szymonwilczek/talos-7/firmware/include/firmware_version.h

#ifndef FIRMWARE_VERSION_H
#define FIRMWARE_VERSION_H

#define FW_VERSION_MAJOR 2
#define FW_VERSION_MINOR 8
#define FW_VERSION_PATCH 0

#define FW_BUILD_DATE "2025-11-23"

#endif // FIRMWARE_VERSION_H
