szymonwilczek/talos-7/firmware/include/easter_egg.h

#ifndef EASTER_EGG_H
#define EASTER_EGG_H

#include <stdbool.h>

/**
 * @brief Runs the Atari Breakout game.
 *
 * Blocking function. Exits when Button 1 is pressed.
 */
void run_game_breakout(void);

#endif // EASTER_EGG_H
