szymonwilczek/talos-7/firmware/include/assets_graphics.h

#ifndef ASSETS_GRAPHICS_H
#define ASSETS_GRAPHICS_H

#include <stdint.h>

// --- TALOS LOGO (8x8 Mini) ---
static const uint8_t talos_logo_8x8[8] = {0x0F, 0x09, 0xFD, 0x01,
                                          0x01, 0xDD, 0x09, 0x0F};

// Talos 7 Favicon (16x16 pixel grid)
static const uint8_t talos_favicon_16x16[] = {
    0x3e, 0x22, 0x22, 0x12, 0x12, 0xf2, 0xf2, 0x00, 0x00, 0xf2, 0xf2,
    0x12, 0x12, 0x22, 0x22, 0x3e, 0x00, 0x00, 0x00, 0x00, 0x00, 0x7f,
    0x7f, 0x00, 0x00, 0x7d, 0x7d, 0x00, 0x00, 0x00, 0x00, 0x00};

// Talos 7 Boot Logo (32x32 pixel grid)
// Format: 4 pages (rows 8px) for 32 columns. Total: 128 bytes.
static const uint8_t talos_boot_logo_32x32[] = {
    // page 0
    0xfc, 0xfc, 0x0c, 0x0c, 0x0c, 0x0c, 0x8c, 0x8c, 0x8c, 0x8c, 0x8c, 0x8c,
    0x8c, 0x8c, 0x00, 0x00, 0x00, 0x00, 0x8c, 0x8c, 0x8c, 0x8c, 0x8c, 0x8c,
    0x8c, 0x8c, 0x0c, 0x0c, 0x0c, 0x0c, 0xfc, 0xfc,
    // page 1
    0x07, 0x07, 0x06, 0x06, 0x06, 0x07, 0x03, 0x01, 0x01, 0x01, 0xff, 0xff,
    0xff, 0xff, 0x00, 0x00, 0x00, 0x00, 0xff, 0xff, 0xff, 0xff, 0x01, 0x01,
    0x01, 0x03, 0x07, 0x06, 0x06, 0x06, 0x07, 0x07,
    // page 2
    0x00, 0x00, 0x00, 0x00, 0x00, 0x00, 0x00, 0x00, 0x00, 0x00, 0xff, 0xff,
    0xff, 0xff, 0x00, 0x00, 0x00, 0x00, 0xf8, 0xf8, 0xf8, 0xf8, 0x00, 0x00,
    0x00, 0x00, 0x00, 0x00, 0x00, 0x00, 0x00, 0x00,
    // page 3
    0x00, 0x00, 0x00, 0x00, 0x00, 0x00, 0x00, 0x00, 0x00, 0x00, 0x7f, 0x7f,
    0x7f, 0x7f, 0x00, 0x00, 0x00, 0x00, 0x7f, 0x7f, 0x7f, 0x7f, 0x00, 0x00,
    0x00, 0x00, 0x00, 0x00, 0x00, 0x00, 0x00, 0x00};

// Space Invaders - Aliens (8x8) - Hands up
static const uint8_t invader_frame1[8] = {0x18, 0x3C, 0x7E, 0xDB,
                                          0xFF, 0x24, 0x5A, 0xA5};

// Space Invaders - Aliens (8x8) - Hands down
static const uint8_t invader_frame2[8] = {0x18, 0x3C, 0x7E, 0xDB,
                                          0xFF, 0x5A, 0x81, 0x42};

// Space Invaders - Cannon (8x8)
static const uint8_t cannon_bitmap[8] = {0x00, 0x00, 0x7E, 0x3C,
                                         0x18, 0x3C, 0x7E, 0x00};

#endif // ASSETS_GRAPHICS_H
