szymonwilczek/talos-7/firmware/include/emoji.h

#ifndef EMOJI_H
#define EMOJI_H

static const uint8_t emoji_bitmaps[21][8] = {
    // 0: 🎮 (controller)
    {0x38, 0x44, 0x94, 0x44, 0x46, 0x95, 0x44, 0x38},
    // 1: 💼 (briefcase)
    {0x7c, 0x46, 0x4a, 0x5a, 0x5a, 0x4a, 0x46, 0x7c},
    // 2: 🏠 (home)
    {0x10, 0xf8, 0x8c, 0xe6, 0x86, 0x8c, 0xf8, 0x10},
    // 3: 🔧 (settings - wrench)
    {0x00, 0x00, 0xc7, 0x7c, 0x7c, 0xc7, 0x00, 0x00},
    // 4: ⚡ (lightning)
    {0x00, 0x80, 0xc8, 0x6c, 0x3e, 0x1b, 0x09, 0x00},
    // 5: 📧 (mail)
    {0x00, 0x3e, 0x41, 0x5d, 0x51, 0x4e, 0x20, 0x00},
    // 6: 💻 (computer)
    {0x3e, 0x22, 0xa2, 0xe2, 0xe2, 0xa2, 0x22, 0x3e},
    // 7: 🎵 (music note)
    {0xc0, 0xfe, 0xc2, 0x02, 0x62, 0x7e, 0x60, 0x00},
    // 8: 📝 (note)
    {0xc0, 0xa0, 0x50, 0x28, 0x1c, 0x0a, 0x07, 0x03},
    // 9: ☕ (coffee cup)
    {0x7e, 0xc2, 0xc2, 0xc2, 0xc2, 0xfe, 0x64, 0x3c},
    // 10: 🗡️ (sword)
    {0xd8, 0xf0, 0x78, 0x7c, 0x5e, 0x0f, 0x07, 0x03},
    // 11: ❤️ (heart)
    {0x00, 0x0c, 0x12, 0x22, 0x44, 0x22, 0x12, 0x0c},
    // 12: 🔔 (bell)
    {0x40, 0x7c, 0xc6, 0xc6, 0x7c, 0x40, 0x00, 0x00},
    // 13: 🧪 (lab probe)
    {0x40, 0xa0, 0x91, 0x8f, 0x8f, 0x91, 0xa0, 0x40},
    // 14: 🔒 (lock)
    {0x78, 0xfe, 0xf9, 0xc9, 0xf9, 0xfe, 0x78, 0x00},
    // 15: ☂️ (umbrella)
    {0x0c, 0x0e, 0x4f, 0x8f, 0x7f, 0x0f, 0x0e, 0x0c},
    // 16: 🦕 (dinosaur)
    {0x06, 0x15, 0xff, 0x7d, 0xff, 0x40, 0x30, 0x00},
    // 17: 👻 (ghost)
    {0x3e, 0x45, 0x47, 0xf5, 0xcf, 0x83, 0x82, 0x84},
    // 18: 🔫 (pistol)
    {0x07, 0x06, 0x06, 0x0e, 0x16, 0x96, 0xfe, 0x7c},
    // 19: ⏳ (hourglass)
    {0x82, 0xee, 0x92, 0x92, 0x92, 0xee, 0x82, 0x00},
    // 20: 🌷 (tulip)
    {0x20, 0x4f, 0x9e, 0xff, 0x9e, 0x4f, 0x20, 0x00},
};

#define MAX_EMOJIS 21
static const char *emoji_strings[MAX_EMOJIS] = {
    "🎮", "💼", "🏠", "🔧", "⚡", "📧", "💻", "🎵", "📝", "☕", "🗡️",
    "❤️",  "🔔", "🧪", "🔒", "☂️",  "🦕", "👻", "🔫", "⏳", "🌷"};

static const uint8_t os_icons[3][8] = {
    // 0: Linux
    {0x20, 0xfe, 0x37, 0x33, 0x3f, 0xf7, 0xf3, 0xff},
    // 1: Windows
    {0x00, 0xee, 0xee, 0xee, 0x00, 0xee, 0xee, 0xee},
    // 2: macOS
    {0x38, 0xfc, 0xfc, 0x7a, 0xfd, 0xfc, 0x48, 0x00},
};

#endif // EMOJI_H
