szymonwilczek/talos-7/firmware/include/tusb_config.h

#ifndef _TUSB_CONFIG_H_
#define _TUSB_CONFIG_H_

#ifdef __cplusplus
extern "C" {
#endif

//--------------------------------------------------------------------+
// Board Specific Configuration
//--------------------------------------------------------------------+

#ifndef BOARD_TUD_RHPORT
#define BOARD_TUD_RHPORT 0
#endif

#ifndef BOARD_TUD_MAX_SPEED
#define BOARD_TUD_MAX_SPEED OPT_MODE_FULL_SPEED
#endif

//--------------------------------------------------------------------+
// COMMON CONFIGURATION
//--------------------------------------------------------------------+

// defined by compiler flags for flexibility
#ifndef CFG_TUSB_MCU
#define CFG_TUSB_MCU OPT_MCU_RP2040
#endif

#ifndef CFG_TUSB_OS
#define CFG_TUSB_OS OPT_OS_NONE
#endif

#ifndef CFG_TUSB_DEBUG
#define CFG_TUSB_DEBUG 0
#endif

#ifndef CFG_TUSB_MEM_SECTION
#define CFG_TUSB_MEM_SECTION
#endif

#ifndef CFG_TUSB_MEM_ALIGN
#define CFG_TUSB_MEM_ALIGN __attribute__((aligned(4)))
#endif

//--------------------------------------------------------------------+
// DEVICE CONFIGURATION
//--------------------------------------------------------------------+

#ifndef CFG_TUD_ENDPOINT0_SIZE
#define CFG_TUD_ENDPOINT0_SIZE 64
#endif

//------------- CLASS -------------//
#define CFG_TUD_HID 1
#define CFG_TUD_CDC 1
#define CFG_TUD_MSC 0
#define CFG_TUD_MIDI 1
#define CFG_TUD_VENDOR 0

// HID buffer size should be sufficient to hold ID (if any) + Data
#define CFG_TUD_HID_EP_BUFSIZE 16

// CDC FIFO size of TX and RX
#define CFG_TUD_CDC_RX_BUFSIZE 256
#define CFG_TUD_CDC_TX_BUFSIZE 256
#define CFG_TUD_MIDI_RX_BUFSIZE 64
#define CFG_TUD_MIDI_TX_BUFSIZE 64

// CDC Endpoint transfer buffer size, more is faster
#define CFG_TUD_CDC_EP_BUFSIZE 64

//--------------------------------------------------------------------+
// DEVICE MODE CONFIGURATION
//--------------------------------------------------------------------+

#define CFG_TUSB_RHPORT0_MODE (OPT_MODE_DEVICE | OPT_MODE_FULL_SPEED)

#ifdef __cplusplus
}
#endif

#endif /* _TUSB_CONFIG_H_ */
