szymonwilczek/talos-7/firmware/tests/test_macro_config.c

/*
 * unit tests for macro_config.c
 *
 * tests: CRC32 algorithm, layer switching logic, factory defaults structure
 *
 * note: this file contains copied logic from macro_config.c to avoid
 * complex mocking of flash/watchdog. i did test the algorithms myself.
 */

#include "unity/unity.h"

#include <stddef.h>
#include <stdint.h>
#include <string.h>

// copied constants from firmware
#define NUM_BUTTONS 7
#define MAX_LAYERS 4
#define MAX_SEQUENCE_STEPS 16
#define MAX_SCRIPT_SIZE 512
#define MAX_LAYER_NAME_LEN 16
#define MAX_MACRO_NAME_LEN 16

// copied macro types
typedef enum {
  MACRO_TYPE_KEY_PRESS = 0,
  MACRO_TYPE_KEY_SEQUENCE = 1,
  MACRO_TYPE_TEXT_STRING = 2,
  MACRO_TYPE_LAYER_TOGGLE = 3,
  MACRO_TYPE_MOUSE_MOVE = 4,
  MACRO_TYPE_MOUSE_CLICK = 5,
  MACRO_TYPE_SCRIPT = 6,
  MACRO_TYPE_MIDI_NOTE = 7,
  MACRO_TYPE_MIDI_CC = 8
} macro_type_t;

// copied key step structure
typedef struct {
  uint8_t keycode;
  uint8_t modifiers;
} key_step_t;

// copied macro entry structure
typedef struct {
  macro_type_t type;
  uint8_t value;
  char macro_string[64];
  char name[MAX_MACRO_NAME_LEN];
  uint8_t emoji_index;
  key_step_t sequence[MAX_SEQUENCE_STEPS];
  uint8_t sequence_length;
  uint8_t repeat_count;
  uint16_t repeat_interval;
  int8_t mouse_x;
  int8_t mouse_y;
  uint8_t midiNote;
  uint8_t midiVelocity;
  uint8_t midiChannel;
  uint8_t midiCCNumber;
  uint8_t midiCCValue;
  char script[MAX_SCRIPT_SIZE];
  uint8_t script_platform;
  key_step_t terminal_shortcut[MAX_SEQUENCE_STEPS];
  uint8_t terminal_shortcut_length;
} macro_entry_t;

// copied config structure
typedef struct {
  macro_entry_t macros[MAX_LAYERS][NUM_BUTTONS];
  char layer_names[MAX_LAYERS][MAX_LAYER_NAME_LEN];
  uint8_t layer_emojis[MAX_LAYERS];
  uint8_t current_layer;
  uint8_t oled_timeout;
  uint32_t crc32;
} config_data_t;

// copied CRC32 table from macro_config.c
static const uint32_t crc32_table[256] = {
    0x00000000, 0x77073096, 0xEE0E612C, 0x990951BA, 0x076DC419, 0x706AF48F,
    0xE963A535, 0x9E6495A3, 0x0EDB8832, 0x79DCB8A4, 0xE0D5E91E, 0x97D2D988,
    0x09B64C2B, 0x7EB17CBD, 0xE7B82D07, 0x90BF1D91, 0x1DB71064, 0x6AB020F2,
    0xF3B97148, 0x84BE41DE, 0x1ADAD47D, 0x6DDDE4EB, 0xF4D4B551, 0x83D385C7,
    0x136C9856, 0x646BA8C0, 0xFD62F97A, 0x8A65C9EC, 0x14015C4F, 0x63066CD9,
    0xFA0F3D63, 0x8D080DF5, 0x3B6E20C8, 0x4C69105E, 0xD56041E4, 0xA2677172,
    0x3C03E4D1, 0x4B04D447, 0xD20D85FD, 0xA50AB56B, 0x35B5A8FA, 0x42B2986C,
    0xDBBBC9D6, 0xACBCF940, 0x32D86CE3, 0x45DF5C75, 0xDCD60DCF, 0xABD13D59,
    0x26D930AC, 0x51DE003A, 0xC8D75180, 0xBFD06116, 0x21B4F4B5, 0x56B3C423,
    0xCFBA9599, 0xB8BDA50F, 0x2802B89E, 0x5F058808, 0xC60CD9B2, 0xB10BE924,
    0x2F6F7C87, 0x58684C11, 0xC1611DAB, 0xB6662D3D, 0x76DC4190, 0x01DB7106,
    0x98D220BC, 0xEFD5102A, 0x71B18589, 0x06B6B51F, 0x9FBFE4A5, 0xE8B8D433,
    0x7807C9A2, 0x0F00F934, 0x9609A88E, 0xE10E9818, 0x7F6A0DBB, 0x086D3D2D,
    0x91646C97, 0xE6635C01, 0x6B6B51F4, 0x1C6C6162, 0x856530D8, 0xF262004E,
    0x6C0695ED, 0x1B01A57B, 0x8208F4C1, 0xF50FC457, 0x65B0D9C6, 0x12B7E950,
    0x8BBEB8EA, 0xFCB9887C, 0x62DD1DDF, 0x15DA2D49, 0x8CD37CF3, 0xFBD44C65,
    0x4DB26158, 0x3AB551CE, 0xA3BC0074, 0xD4BB30E2, 0x4ADFA541, 0x3DD895D7,
    0xA4D1C46D, 0xD3D6F4FB, 0x4369E96A, 0x346ED9FC, 0xAD678846, 0xDA60B8D0,
    0x44042D73, 0x33031DE5, 0xAA0A4C5F, 0xDD0D7CC9, 0x5005713C, 0x270241AA,
    0xBE0B1010, 0xC90C2086, 0x5768B525, 0x206F85B3, 0xB966D409, 0xCE61E49F,
    0x5EDEF90E, 0x29D9C998, 0xB0D09822, 0xC7D7A8B4, 0x59B33D17, 0x2EB40D81,
    0xB7BD5C3B, 0xC0BA6CAD, 0xEDB88320, 0x9ABFB3B6, 0x03B6E20C, 0x74B1D29A,
    0xEAD54739, 0x9DD277AF, 0x04DB2615, 0x73DC1683, 0xE3630B12, 0x94643B84,
    0x0D6D6A3E, 0x7A6A5AA8, 0xE40ECF0B, 0x9309FF9D, 0x0A00AE27, 0x7D079EB1,
    0xF00F9344, 0x8708A3D2, 0x1E01F268, 0x6906C2FE, 0xF762575D, 0x806567CB,
    0x196C3671, 0x6E6B06E7, 0xFED41B76, 0x89D32BE0, 0x10DA7A5A, 0x67DD4ACC,
    0xF9B9DF6F, 0x8EBEEFF9, 0x17B7BE43, 0x60B08ED5, 0xD6D6A3E8, 0xA1D1937E,
    0x38D8C2C4, 0x4FDFF252, 0xD1BB67F1, 0xA6BC5767, 0x3FB506DD, 0x48B2364B,
    0xD80D2BDA, 0xAF0A1B4C, 0x36034AF6, 0x41047A60, 0xDF60EFC3, 0xA867DF55,
    0x316E8EEF, 0x4669BE79, 0xCB61B38C, 0xBC66831A, 0x256FD2A0, 0x5268E236,
    0xCC0C7795, 0xBB0B4703, 0x220216B9, 0x5505262F, 0xC5BA3BBE, 0xB2BD0B28,
    0x2BB45A92, 0x5CB36A04, 0xC2D7FFA7, 0xB5D0CF31, 0x2CD99E8B, 0x5BDEAE1D,
    0x9B64C2B0, 0xEC63F226, 0x756AA39C, 0x026D930A, 0x9C0906A9, 0xEB0E363F,
    0x72076785, 0x05005713, 0x95BF4A82, 0xE2B87A14, 0x7BB12BAE, 0x0CB61B38,
    0x92D28E9B, 0xE5D5BE0D, 0x7CDCEFB7, 0x0BDBDF21, 0x86D3D2D4, 0xF1D4E242,
    0x68DDB3F8, 0x1FDA836E, 0x81BE16CD, 0xF6B9265B, 0x6FB077E1, 0x18B74777,
    0x88085AE6, 0xFF0F6A70, 0x66063BCA, 0x11010B5C, 0x8F659EFF, 0xF862AE69,
    0x616BFFD3, 0x166CCF45, 0xA00AE278, 0xD70DD2EE, 0x4E048354, 0x3903B3C2,
    0xA7672661, 0xD06016F7, 0x4969474D, 0x3E6E77DB, 0xAED16A4A, 0xD9D65ADC,
    0x40DF0B66, 0x37D83BF0, 0xA9BCAE53, 0xDEBB9EC5, 0x47B2CF7F, 0x30B5FFE9,
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

// copied CRC calculation function
static uint32_t test_calculate_crc(const config_data_t *config) {
  uint32_t crc = 0xFFFFFFFF;
  const uint8_t *data = (const uint8_t *)config;
  size_t len = offsetof(config_data_t, crc32);

  for (size_t i = 0; i < len; i++) {
    crc = crc32_table[(crc ^ data[i]) & 0xFF] ^ (crc >> 8);
  }

  return ~crc;
}

// layer switching simulation
static uint8_t g_test_layer = 0;

static uint8_t test_get_layer(void) { return g_test_layer; }

static void test_cycle_layer(void) {
  g_test_layer = (g_test_layer + 1) % MAX_LAYERS;
}

static void test_set_layer(uint8_t layer) {
  if (layer < MAX_LAYERS) {
    g_test_layer = layer;
  }
}

// factory defaults simulation
static void test_set_factory_defaults(config_data_t *config) {
  memset(config, 0, sizeof(config_data_t));

  // set layer names
  snprintf(config->layer_names[0], MAX_LAYER_NAME_LEN, "Main");
  snprintf(config->layer_names[1], MAX_LAYER_NAME_LEN, "Work");
  snprintf(config->layer_names[2], MAX_LAYER_NAME_LEN, "Home");
  snprintf(config->layer_names[3], MAX_LAYER_NAME_LEN, "Media");

  // set emojis
  config->layer_emojis[0] = 0;
  config->layer_emojis[1] = 1;
  config->layer_emojis[2] = 2;
  config->layer_emojis[3] = 7;

  // button 7 (index 6) is layer toggle
  for (int layer = 0; layer < MAX_LAYERS; layer++) {
    config->macros[layer][6].type = MACRO_TYPE_LAYER_TOGGLE;
  }

  config->oled_timeout = 60;
}

// ==================== CRC32 TESTS ====================

void test_crc32_nonzero_for_zeroed_config(void) {
  config_data_t config;
  memset(&config, 0, sizeof(config));

  uint32_t crc = test_calculate_crc(&config);

  // crc of zeroed data should still produce a valid checksum
  TEST_ASSERT_TRUE(crc != 0);
}

void test_crc32_different_for_different_data(void) {
  config_data_t config1;
  config_data_t config2;

  memset(&config1, 0, sizeof(config1));
  memset(&config2, 0, sizeof(config2));

  config2.current_layer = 1;

  uint32_t crc1 = test_calculate_crc(&config1);
  uint32_t crc2 = test_calculate_crc(&config2);

  TEST_ASSERT_NOT_EQUAL(crc1, crc2);
}

void test_crc32_same_for_identical_data(void) {
  config_data_t config1;
  config_data_t config2;

  memset(&config1, 0xAB, sizeof(config1));
  memset(&config2, 0xAB, sizeof(config2));

  uint32_t crc1 = test_calculate_crc(&config1);
  uint32_t crc2 = test_calculate_crc(&config2);

  TEST_ASSERT_EQUAL(crc1, crc2);
}

void test_crc32_changes_with_any_byte(void) {
  config_data_t config1;
  config_data_t config2;

  memset(&config1, 0, sizeof(config1));
  memset(&config2, 0, sizeof(config2));

  // change just one byte in macro name
  config2.macros[0][0].name[0] = 'X';

  uint32_t crc1 = test_calculate_crc(&config1);
  uint32_t crc2 = test_calculate_crc(&config2);

  TEST_ASSERT_NOT_EQUAL(crc1, crc2);
}

void test_crc32_ignores_crc_field(void) {
  config_data_t config1;
  config_data_t config2;

  memset(&config1, 0, sizeof(config1));
  memset(&config2, 0, sizeof(config2));

  // only difference is in crc32 field itself
  config1.crc32 = 0x12345678;
  config2.crc32 = 0xDEADBEEF;

  uint32_t crc1 = test_calculate_crc(&config1);
  uint32_t crc2 = test_calculate_crc(&config2);

  // crc calculation should ignore the crc32 field
  TEST_ASSERT_EQUAL(crc1, crc2);
}

// ==================== LAYER SWITCHING TESTS ====================

void test_layer_starts_at_zero(void) {
  g_test_layer = 0;
  TEST_ASSERT_EQUAL(0, test_get_layer());
}

void test_layer_cycle_increments(void) {
  g_test_layer = 0;

  test_cycle_layer();
  TEST_ASSERT_EQUAL(1, test_get_layer());

  test_cycle_layer();
  TEST_ASSERT_EQUAL(2, test_get_layer());

  test_cycle_layer();
  TEST_ASSERT_EQUAL(3, test_get_layer());
}

void test_layer_cycle_wraps_at_max(void) {
  g_test_layer = 0;

  for (int i = 0; i < MAX_LAYERS; i++) {
    test_cycle_layer();
  }

  TEST_ASSERT_EQUAL(0, test_get_layer());
}

void test_layer_set_valid(void) {
  test_set_layer(2);
  TEST_ASSERT_EQUAL(2, test_get_layer());
}

void test_layer_set_invalid_ignored(void) {
  g_test_layer = 1;
  test_set_layer(10); // invalid
  TEST_ASSERT_EQUAL(1, test_get_layer());
}

// ==================== FACTORY DEFAULTS TESTS ====================

void test_factory_defaults_sets_layer_names(void) {
  config_data_t config;
  test_set_factory_defaults(&config);

  TEST_ASSERT_EQUAL_STRING("Main", config.layer_names[0]);
  TEST_ASSERT_EQUAL_STRING("Work", config.layer_names[1]);
  TEST_ASSERT_EQUAL_STRING("Home", config.layer_names[2]);
  TEST_ASSERT_EQUAL_STRING("Media", config.layer_names[3]);
}

void test_factory_defaults_button7_is_layer_toggle(void) {
  config_data_t config;
  test_set_factory_defaults(&config);

  for (int layer = 0; layer < MAX_LAYERS; layer++) {
    TEST_ASSERT_EQUAL(MACRO_TYPE_LAYER_TOGGLE, config.macros[layer][6].type);
  }
}

void test_factory_defaults_sequence_length_zero(void) {
  config_data_t config;
  test_set_factory_defaults(&config);

  for (int layer = 0; layer < MAX_LAYERS; layer++) {
    for (int btn = 0; btn < NUM_BUTTONS; btn++) {
      TEST_ASSERT_EQUAL(0, config.macros[layer][btn].sequence_length);
    }
  }
}

void test_factory_defaults_oled_timeout(void) {
  config_data_t config;
  test_set_factory_defaults(&config);

  TEST_ASSERT_EQUAL(60, config.oled_timeout);
}

void test_factory_defaults_current_layer_zero(void) {
  config_data_t config;
  test_set_factory_defaults(&config);

  TEST_ASSERT_EQUAL(0, config.current_layer);
}

// ==================== STRUCTURE TESTS ====================

void test_config_size_reasonable(void) {
  // config should fit in flash sector
  TEST_ASSERT_TRUE(sizeof(config_data_t) < 64 * 1024);
}

void test_macro_entry_size(void) {
  // sanity check that macro entry is not too large
  TEST_ASSERT_TRUE(sizeof(macro_entry_t) < 1024);
}

// ==================== RUNNER ====================

void run_macro_config_tests(void) {
  printf("\n=== Macro Config Tests ===\n");

  // crc tests
  RUN_TEST(test_crc32_nonzero_for_zeroed_config);
  RUN_TEST(test_crc32_different_for_different_data);
  RUN_TEST(test_crc32_same_for_identical_data);
  RUN_TEST(test_crc32_changes_with_any_byte);
  RUN_TEST(test_crc32_ignores_crc_field);

  // layer switching tests
  RUN_TEST(test_layer_starts_at_zero);
  RUN_TEST(test_layer_cycle_increments);
  RUN_TEST(test_layer_cycle_wraps_at_max);
  RUN_TEST(test_layer_set_valid);
  RUN_TEST(test_layer_set_invalid_ignored);

  // factory defaults tests
  RUN_TEST(test_factory_defaults_sets_layer_names);
  RUN_TEST(test_factory_defaults_button7_is_layer_toggle);
  RUN_TEST(test_factory_defaults_sequence_length_zero);
  RUN_TEST(test_factory_defaults_oled_timeout);
  RUN_TEST(test_factory_defaults_current_layer_zero);

  // structure tests
  RUN_TEST(test_config_size_reasonable);
  RUN_TEST(test_macro_entry_size);
}
